chnyifei/digital-colour-palette/hardware/colourPalette.kicad_sch

## KiCad design hardware/colourPalette.kicad_sch (2026-08-23)

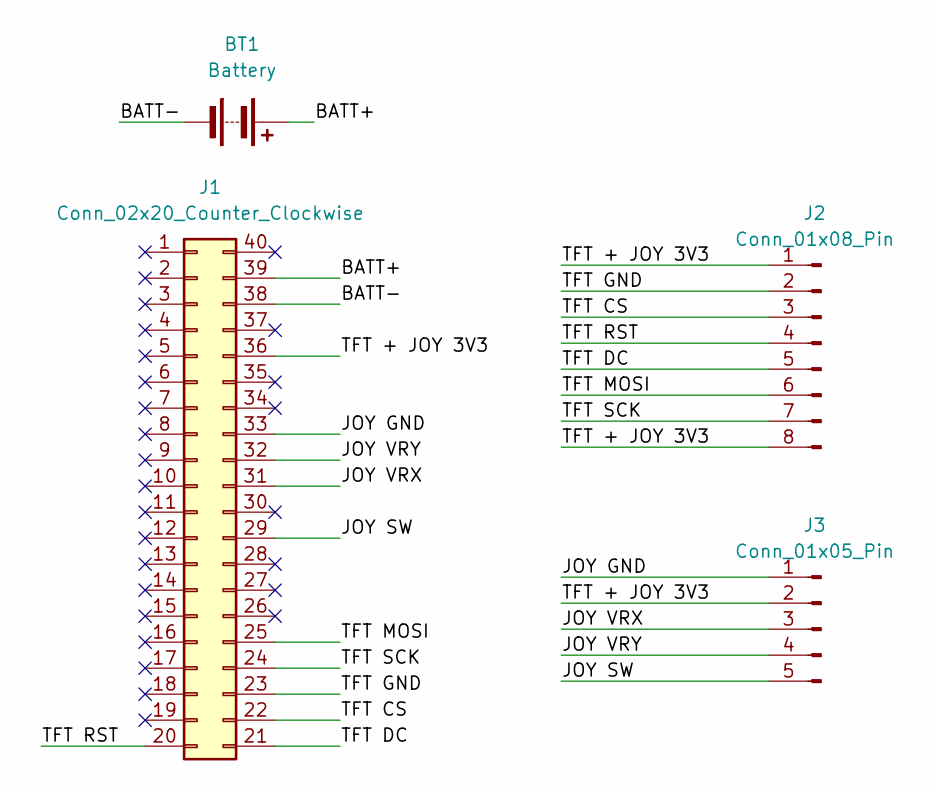
[picture p7: schematic colourPalette.kicad_sch]

Parts:
BT1: Battery
J1: Conn_02x20_Counter_Clockwise
J2: Conn_01x08_Pin
J3: Conn_01x05_Pin

Connections:
BATT+: BT1.1 (+), J1.39
BATT-: BT1.2 (-), J1.38
JOY GND: J1.33, J3.1
JOY SW: J1.29, J3.5
JOY VRX: J1.31, J3.3
JOY VRY: J1.32, J3.4
TFT + JOY 3V3: J1.36, J2.1, J2.8, J3.2
TFT CS: J1.22, J2.3
TFT DC: J1.21, J2.5
TFT GND: J1.23, J2.2
TFT MOSI: J1.25, J2.6
TFT RST: J1.20, J2.4
TFT SCK: J1.24, J2.7
