chnyifei/digital-colour-palette/src/paintPaletteIcon.h

// paintPalette1__1_  120 x 132  (RGB565)
const uint16_t paintPalette1__1_[] PROGMEM = {
  0xF816, 0xF816, 0xF816, 0xF816, 0xF816, 0xF816, 0xF816, 0xF816, 0xF816, 0xF816, 0xF816, 0xF816,
  0xF816, 0xF816, 0xF816, 0xF816, 0xF816, 0xF816, 0xF816, 0xF816, 0xF816, 0xF816, 0xF816, 0xF816,
  0xF816, 0xF816, 0xF816, 0xF816, 0xF816, 0xF816, 0xF816, 0xF816, 0xF816, 0xF816, 0xF816, 0xF816,
  0xF816, 0xF816, 0xF816, 0xF816, 0xF816, 0xF816, 0xF816, 0xF816, 0xF816, 0xF816, 0xF816, 0xF816,
  0xF816, 0xF816, 0xF816, 0xF816, 0xF816, 0xF816, 0xF816, 0xF816, 0xF816, 0xF816, 0xF816, 0xF816,
  0xF816, 0xF816, 0xF816, 0xF816, 0xF816, 0xF816, 0xF816, 0xF816, 0xF816, 0xF816, 0xF816, 0xF816,
  0xF816, 0xF816, 0xF816, 0xF816, 0xF816, 0xF816, 0xF816, 0xF816, 0xF816, 0xF816, 0xF816, 0xF816,
  0xF816, 0xF816, 0xF816, 0xF816, 0xF816, 0xF816, 0xB5B6, 0xF816, 0xF816, 0xF816, 0xF816, 0xB5B6,
  0xF816, 0xF816, 0xF816, 0xB5B6, 0xF816, 0xF816, 0xB5B6, 0xF816, 0xF816, 0xF816, 0xF816, 0xF816,
  0xF816, 0xF816, 0xF816, 0xF816, 0xF816, 0xF816, 0xF816, 0xF816, 0xF816, 0xF816, 0xF816, 0xF816,
  0xF816, 0xF816, 0xF816, 0xF816, 0xF816, 0xF816, 0xF816, 0xF816, 0xF816, 0xF816, 0xF816, 0xF816,
  0xF816, 0xF816, 0xF816, 0xF816, 0xF816, 0xF816, 0xF816, 0xF816, 0xF816, 0xF816, 0xF816, 0xF816,
  0xF816, 0xF816, 0xF816, 0xF816, 0xF816, 0xF816, 0xF816, 0xF816, 0xF816, 0xF816, 0xF816, 0xF816,
  0xF816, 0xF816, 0xF816, 0xF816, 0xF816, 0xF816, 0xF816, 0xF816, 0xF816, 0xF816, 0xF816, 0xF816,
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
  0xF816, 0xB5B6, 0xF816, 0xF816, 0xF816, 0xF816, 0xF816, 0xF816, 0xB5B6, 0xF816, 0xF816, 0xF816,
  0xF816, 0xF816, 0xF816, 0xF816, 0xF816, 0xF816, 0xF816, 0xF816, 0xF816, 0xF816, 0xF816, 0xF816,
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
};
const int paintPalette1__1__width  = 120;
const int paintPalette1__1__height = 132;
